WillCallahan/DataLake/collectors/SimpleSensor/firmware/SimpleSensor.X/settings.h

/* 
 * File: settings.h
 * Author: William Callahan
 * Comments: Device settings common for the SimpleSensor project
 * Revision history:
 */
#ifndef XC_HEADER_TEMPLATE_H
#define	XC_HEADER_TEMPLATE_H

#ifdef	__cplusplus
extern "C" {
#endif /* __cplusplus */

#ifndef _XTAL_FREQ
//#define _XTAL_FREQ 31250
#define _XTAL_FREQ 4000000
#endif

#ifdef	__cplusplus
}
#endif /* __cplusplus */

#endif	/* XC_HEADER_TEMPLATE_H */
